jfdelnero/Apollo_7_Squale/hardware/Motherboard/LTspice/squale_modem_filter.asc

C1: cap; 100nF
C2: cap; 68pF
C3: cap; 100nF
C4: cap; 100nF
D1: diode; 1N4148
D2: diode; 1N4148
R1: res; 10K
R2: res; 330K
R3: res; 47K
R4: res; 10K
R5: res; 47K
U1: ADTL084
U2: ADTL084
V1: voltage; 5; Rser=0
V2: voltage; 5; Rser=0
V3: voltage; SINE(0); AC 1
Named nets: 0
.ac oct 10000 1 1000000
