jfdelnero/Apollo_7_Squale/examples/Squale_Technical_Demo/demo_dotschaos_part.c

///////////////////////////////////////////////////////////////////////////////////
//-------------------------------------------------------------------------------//
//-------------------------------------------------------------------------------//
//-----------H----H--X----X-----CCCCC----22222----0000-----0000------11----------//
//----------H----H----X-X-----C--------------2---0----0---0----0--1--1-----------//
//---------HHHHHH-----X------C----------22222---0----0---0----0-----1------------//
//--------H----H----X--X----C----------2-------0----0---0----0-----1-------------//
//-------H----H---X-----X---CCCCC-----222222----0000-----0000----1111------------//
//-------------------------------------------------------------------------------//
//----------------------------------------------------- http://hxc2001.free.fr --//
///////////////////////////////////////////////////////////////////////////////////
//
// Apollo Squale Technical demo
// A demo for the French Apollo Squale computer.
//
// (c) 2019 HxC2001 / Jean-François DEL NERO
// (c) 2019 MO5.COM / Association MO5.COM
//
// Written by: Jean François DEL NERO
//
// You are free to do what you want with this code.
// But a credit is always appreciated :)
//
// Change History (most recent first):
///////////////////////////////////////////////////////////////////////////////////

#include <stdint.h>
#include <squale_hw.h>

#include "demo.h"

#include "asm_funcs.h"

#include "deuxd_func.h"

#include "images/footpage.h"

#define BOX_CORNER_POINT1_X 5
#define BOX_CORNER_POINT1_Y 40

#define BOX_CORNER_POINT3_X SCREEN_XSIZE - 5
#define BOX_CORNER_POINT3_Y SCREEN_YSIZE - 5

void demo_dotschaos_part()
{
	#define NB_MAX_POINTS 26
	int i;
	uint8_t p,t;
	uint8_t points[3 * NB_MAX_POINTS];
	uint8_t *tmp_ptr;
	uint8_t nbpoints;

	WAIT_EF9365_READY();
	WR_BYTE( HW_CTLHRD_REG, 7 | ledclavier);
	WR_BYTE( HW_EF9365 + 0x0, 0x0C ); // Clear screen

	WAIT_EF9365_READY();

	display_vectsprite((unsigned char *) &bmp_data_footpage, 0, SCREEN_YSIZE-33 );

	WR_BYTE( HW_CTLHRD_REG, 3 | ledclavier);

	Box(BOX_CORNER_POINT1_X, BOX_CORNER_POINT1_Y, BOX_CORNER_POINT3_X, BOX_CORNER_POINT3_Y);

	printstr("Squale technical demo v1.1 (02 Nov 2019)",BOX_CORNER_POINT1_X,BOX_CORNER_POINT1_Y - 9 ,0x11,0x04);
	printstr("Code: Jean-Francois DEL NERO",BOX_CORNER_POINT1_X,BOX_CORNER_POINT1_Y - 18 ,0x11,0x04);
	printstr("Music: Jochen Hippel",BOX_CORNER_POINT1_X,BOX_CORNER_POINT1_Y - 27 ,0x11,0x04);

	nbpoints = 1;

	tmp_ptr = (uint8_t *)&points;

	for(p=0;p<(sizeof(points)/3);p++)
	{
		tmp_ptr[0] = (SCREEN_XSIZE/2) + p*3 + p - 32 ;
		tmp_ptr[1] = SCREEN_YSIZE/2 + ((p*2) * (-1 * (p&1)) - p/2  );
		tmp_ptr[2] = p & 3;
		tmp_ptr += 3;
	}

	i = 0;
	do
	{
		vblank();

		tmp_ptr = (uint8_t *)&points;
		for(p=0;p<nbpoints;p++)
		{
			if(tmp_ptr[2] & 0x1)
				tmp_ptr[0]--;
			else
				tmp_ptr[0]++;

			if(tmp_ptr[2] & 0x2)
				tmp_ptr[1]--;
			else
				tmp_ptr[1]++;

			if(tmp_ptr[0] >=  (BOX_CORNER_POINT3_X - 1) )
				tmp_ptr[2] |= 0x1;

			if(tmp_ptr[0] <=  (BOX_CORNER_POINT1_X + 1) )
				tmp_ptr[2] &= ~0x1;

			if(tmp_ptr[1] >=  (BOX_CORNER_POINT3_Y - 1) )
				tmp_ptr[2] |= 0x2;

			if(tmp_ptr[1] <=  (BOX_CORNER_POINT1_Y + 1) )
				tmp_ptr[2] &= ~0x2;

			tmp_ptr += 3;
		}

		tmp_ptr = (uint8_t *)&points;

		for(p=0;p<nbpoints;p++)
		{
			t = p;
			if( (t&7) == 0x7 )
				t++;
			WR_BYTE( HW_CTLHRD_REG, (t & 15) | ledclavier);
			LigneFast( tmp_ptr[0] , tmp_ptr[1], tmp_ptr[0] , tmp_ptr[1]);
			tmp_ptr += 3;
		}

		i++;

		if(nbpoints<NB_MAX_POINTS)
			nbpoints = 1 + (i / 16);

		if(nbpoints > NB_MAX_POINTS)
			nbpoints = NB_MAX_POINTS;

	}while( new_trigger == old_trigger );
}
