jfdelnero/Apollo_7_Squale/examples/Squale_Technical_Demo/deuxd_func.c

///////////////////////////////////////////////////////////////////////////////////
//-------------------------------------------------------------------------------//
//-------------------------------------------------------------------------------//
//-----------H----H--X----X-----CCCCC----22222----0000-----0000------11----------//
//----------H----H----X-X-----C--------------2---0----0---0----0--1--1-----------//
//---------HHHHHH-----X------C----------22222---0----0---0----0-----1------------//
//--------H----H----X--X----C----------2-------0----0---0----0-----1-------------//
//-------H----H---X-----X---CCCCC-----222222----0000-----0000----1111------------//
//-------------------------------------------------------------------------------//
//----------------------------------------------------- http://hxc2001.free.fr --//
///////////////////////////////////////////////////////////////////////////////////
//
// Apollo Squale Technical demo
// A demo for the French Apollo Squale computer.
//
// (c) 2019 HxC2001 / Jean-François DEL NERO
// (c) 2019 MO5.COM / Association MO5.COM
//
// Written by: Jean François DEL NERO
//
// You are free to do what you want with this code.
// But a credit is always appreciated :)
//
// Change History (most recent first):
///////////////////////////////////////////////////////////////////////////////////

#include <stdint.h>
#include <squale_hw.h>

#include "deuxd_func.h"

void LigneFast(uint8_t x1, uint8_t y1, uint8_t x2, uint8_t y2)
{
	unsigned char cmd;
	uint8_t xlen,ylen;


	if( x1 > x2 )
	{
		cmd = 0x11 | 0x2;
		xlen = x1 - x2;
	}
	else
	{
		cmd = 0x11;
		xlen = x2 - x1;
	}

	if( y1 > y2 )
	{
		cmd = cmd | 0x04;
		ylen = y1 - y2;
	}
	else
	{
		ylen = y2 - y1;
	}

	WAIT_EF9365_READY();

	WR_BYTE( HW_EF9365 + 0x8, 0 );
	WR_BYTE( HW_EF9365 + 0x9, x1 );
	WR_BYTE( HW_EF9365 + 0xA, 0 );
	WR_BYTE( HW_EF9365 + 0xB, y1 );
	WR_BYTE( HW_EF9365 + 0x5, xlen );
	WR_BYTE( HW_EF9365 + 0x7, ylen );
	WR_BYTE( HW_EF9365 + 0x0, cmd );
}

void Box(uint8_t x1, uint8_t y1, uint8_t x2, uint8_t y2)
{
	LigneFast(x1, y1, x2, y1);
	LigneFast(x1, y1, x1, y2);
	LigneFast(x2, y2, x1, y2);
	LigneFast(x2, y2, x2, y1);
}

/*
void cercle(int16_t rayon,int16_t x_centre,int16_t y_centre,uint8_t state)
{
	int16_t x,y,d;

	x=0;
	y=rayon;
	d=rayon;
	while(y>=x)
	{
		setpixel(x+x_centre , y+y_centre,state);
		setpixel(y+x_centre , x+y_centre,state);
		setpixel(-x+x_centre , y+y_centre,state);
		setpixel(-y+x_centre , x+y_centre,state);
		setpixel(x+x_centre , -y+y_centre,state);
		setpixel(y+x_centre , -x+y_centre,state);
		setpixel(-x+x_centre , -y+y_centre,state);
		setpixel(-y+x_centre , -x+y_centre,state);

		if(d >= 2*x)
		{
			d=d-2*x-1;
			x++;
		}
		else
		{
			if( d < 2*(rayon-y) )
			{
				d=d+2*y-1;
				y--;

			}
			else
			{
				d=d+2*(y-x-1);
				y--;
				x++;
			}
		}
	}
	return;
}
*/

extern unsigned char ledclavier;

void display_vectsprite(unsigned char * vectorized_sprite, unsigned char x, unsigned char y)
{
	unsigned char i,j;

	unsigned char nb_lines;
	unsigned char nb_vects;
	unsigned char cnt,color;
	uint8_t  regsbuf[2];
	// [NUMBER_OF_LINES] [NUMBER_OF_VECTORS] [ _CNT|_COL] [ _CNT|_COL] [ _CNT|_COL] [ COUNT__ (if CNT==0)] ... [NUMBER_OF_VECTORS]....

	nb_lines = *vectorized_sprite++;

	WAIT_EF9365_READY();

	WR_BYTE(HW_EF9365 + 0x7, 0x00);

	for(i=0;i<nb_lines;i++)
	{
		regsbuf[0] = x;
		regsbuf[1] = (255 - (y + i));

		WAIT_EF9365_READY();

		WR_BYTE(HW_EF9365 + 0x8,0);
		WR_BYTE(HW_EF9365 + 0x9,regsbuf[0]);
		WR_BYTE(HW_EF9365 + 0xA,0);
		WR_BYTE(HW_EF9365 + 0xB,regsbuf[1]);

		nb_vects = *vectorized_sprite++;
		j = nb_vects;
		do
		{
			color = *vectorized_sprite++;
			cnt = (color >> 4);

			if(!cnt)
				regsbuf[0] = *vectorized_sprite++;
			else
				regsbuf[0] = cnt;
			regsbuf[1] = (color&0xF) | ledclavier;

			WAIT_EF9365_READY();

			WR_BYTE(HW_EF9365 + 0x5, regsbuf[0]);
			WR_BYTE(HW_CTLHRD_REG,   regsbuf[1]);
			WR_BYTE(HW_EF9365 + 0x0, 0x11);

			j--;
		}while(j);
	}
}

void printstr(char * str,unsigned char x,unsigned char y,unsigned char csize,unsigned char color)
{
	volatile unsigned char * ptr;

	ptr = (volatile unsigned char *)HW_EF9365;

	WAIT_EF9365_READY();

	WR_BYTE( HW_CTLHRD_REG, color | ledclavier);

	ptr[0x8] = 0;
	ptr[0x9] = x;
	ptr[0xA] = 0;
	ptr[0xB] = y;

	ptr[0x3] = csize;

	while(*str)
	{
		WAIT_EF9365_READY();
		WR_BYTE( HW_EF9365 + 0x0, *str++ );
	}
}
