jfdelnero/Apollo_7_Squale/examples/Squale_Technical_Demo/cossintab.h

///////////////////////////////////////////////////////////////////////////////////
//-------------------------------------------------------------------------------//
//-------------------------------------------------------------------------------//
//-----------H----H--X----X-----CCCCC----22222----0000-----0000------11----------//
//----------H----H----X-X-----C--------------2---0----0---0----0--1--1-----------//
//---------HHHHHH-----X------C----------22222---0----0---0----0-----1------------//
//--------H----H----X--X----C----------2-------0----0---0----0-----1-------------//
//-------H----H---X-----X---CCCCC-----222222----0000-----0000----1111------------//
//-------------------------------------------------------------------------------//
//----------------------------------------------------- http://hxc2001.free.fr --//
///////////////////////////////////////////////////////////////////////////////////
//
// Apollo Squale Technical demo
// A demo for the French Apollo Squale computer.
//
// (c) 2019 HxC2001 / Jean-François DEL NERO
// (c) 2019 MO5.COM / Association MO5.COM
//
// Written by: Jean François DEL NERO
//
// You are free to do what you want with this code.
// But a credit is always appreciated :)
//
// Change History (most recent first):
///////////////////////////////////////////////////////////////////////////////////

const int8_t SinCos[]=
{
	0,3,6,9,12,15,18,21,24,28,31,34,37,
	40,42,45,48,51,54,57,60,62,65,68,70,
	73,75,78,80,83,85,87,90,92,94,96,98,
	100,102,104,105,107,109,110,112,113,
	115,116,117,118,119,120,121,122,123,
	124,124,125,126,126,126,127,127,127,
	127,127,127,127,126,126,126,125,125,
	124,123,122,122,121,120,118,117,116,
	115,113,112,111,109,107,106,104,102,
	100,98,96,94,92,90,88,85,83,81,78,76,
	73,71,68,65,63,60,57,54,52,49,46,43,40,
	37,34,31,28,25,22,19,16,13,9,6,3,0,
	-3,-6,-9,-12,-15,-19,-22,-25,-28,-31,-34,
	-37,-40,-43,-46,-48,-51,-54,-57,-60,-62,
	-65,-68,-70,-73,-76,-78,-80,-83,-85,-87,
	-90,-92,-94,-96,-98,-100,-102,-104,-106,-107,
	-109,-110,-112,-113,-115,-116,-117,-118,-120,
	-121,-121,-122,-123,-124,-125,-125,-126,-126,
	-126,-127,-127,-127,-127,-127,-127,-127,-126,
	-126,-126,-125,-125,-124,-123,-122,-122,-121,
	-120,-119,-117,-116,-115,-114,-112,-111,-109,
	-107,-106,-104,-102,-100,-98,-96,-94,-92,-90,
	-88,-85,-83,-81,-78,-76,-73,-71,-68,-66,-63,
	-60,-57,-55,-52,-49,-46,-43,-40,-37,-34,-31,
	-28,-25,-22,-19,-16,-13,-10,-7,-3,0
};
