jfdelnero/Apollo_7_Squale/examples/Squale_Technical_Demo/bmp2vect/bmp_file.h

#pragma pack(1)

typedef struct bitmap_data_
{
	int16_t xsize;
	int16_t ysize;
	int16_t nb_color;
	uint8_t * palette;
	uint32_t  * data;
}bitmap_data;

typedef struct tagBITMAPFILEHEADER {
	uint16_t   bfType;
	uint32_t   bfSize;
	uint16_t   bfReserved1;
	uint16_t   bfReserved2;
	uint32_t   bfOffBits;
} BITMAPFILEHEADER;

typedef struct tagBITMAPINFOHEADER {
	uint32_t    biSize;
	uint32_t    biWidth;
	uint32_t    biHeight;
	uint16_t    biPlanes;
	uint16_t    biBitCount;
	uint32_t    biCompression;
	uint32_t    biSizeImage;
	uint32_t    biXPelsPerMeter;
	uint32_t    biYPelsPerMeter;
	uint32_t    biClrUsed;
	uint32_t    biClrImportant;
} BITMAPINFOHEADER;

typedef struct tagRGBQUAD {
	uint8_t rgbBlue;
	uint8_t rgbGreen;
	uint8_t rgbRed;
	uint8_t rgbReserved;
} RGBQUAD;

#pragma pack()

int bmp_load(char * file,bitmap_data * bdata);
int bmpRLE8b_write(char * file,bitmap_data * bdata);
int bmp24b_write(char * file,bitmap_data * bdata);
int bmp16b_write(char * file,bitmap_data * bdata);
